fachat/csa_ultracpu/Board/csa_ultracpu-v2.0b-sch-6.png

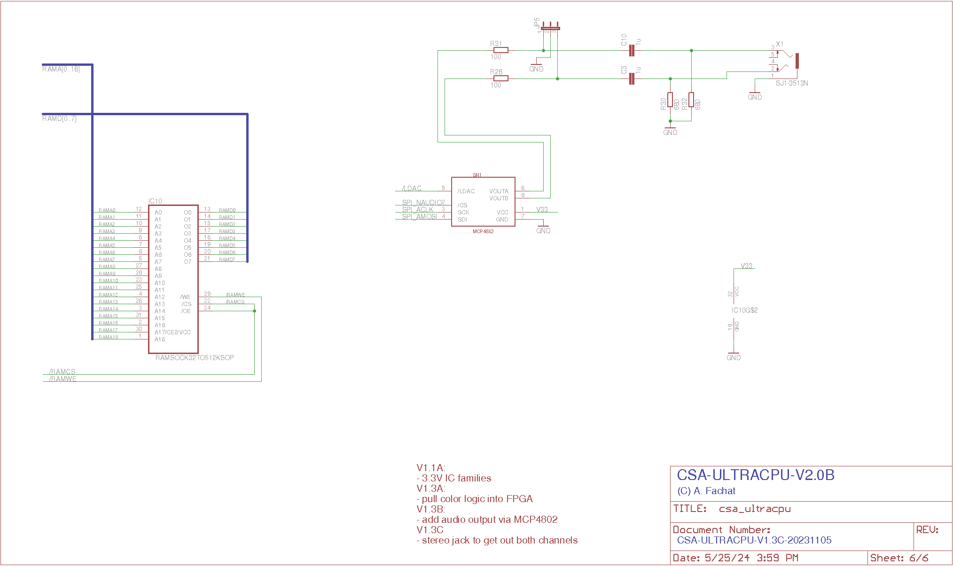
Board/csa_ultracpu-v2.0b-sch-6.png
